icegoat9/humidity_eink/docs/humidity18_in_case.JPG

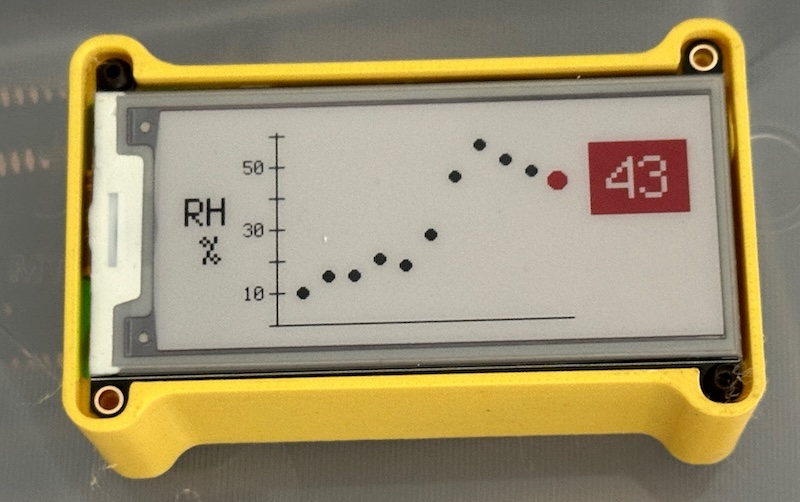
docs/humidity18_in_case.JPG
