icegoat9/humidity_eink/docs/screenshot_3dprint_case_paths.png

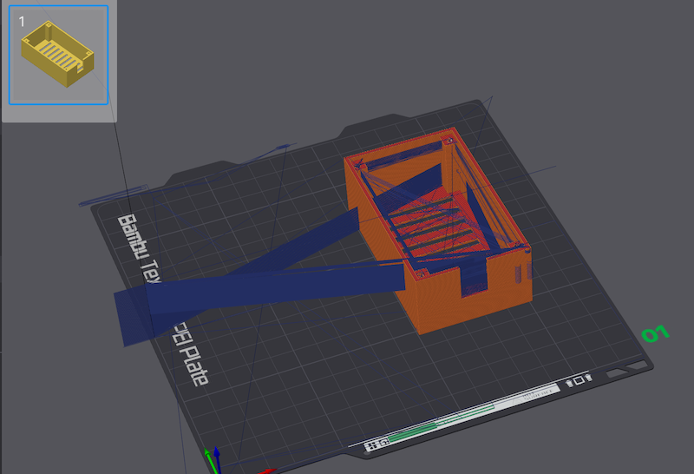
docs/screenshot_3dprint_case_paths.png
