icegoat9/humidity_eink/code.py

import main_humidity_eink
#import experiments.test_led
#import experiments.adafruit_il0373_demo
#import experiments.test_eink_display
#import experiments.test_sparkline
#import experiments.test_graph_design
#import experiments.test_box_graph
